qwelyt/scorne/hardware/IDC_2x5p.stl

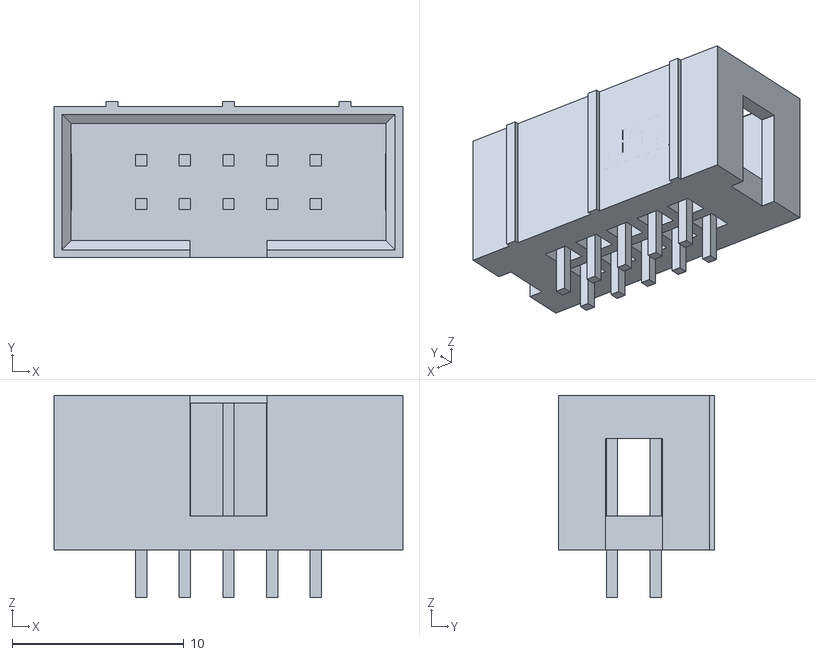
[picture p16: CAD file, 2021-04-13]
hardware/IDC_2x5p.stl
20.3 x 9.10 x 11.8
