qwelyt/scorne/hardware/scorne.stl

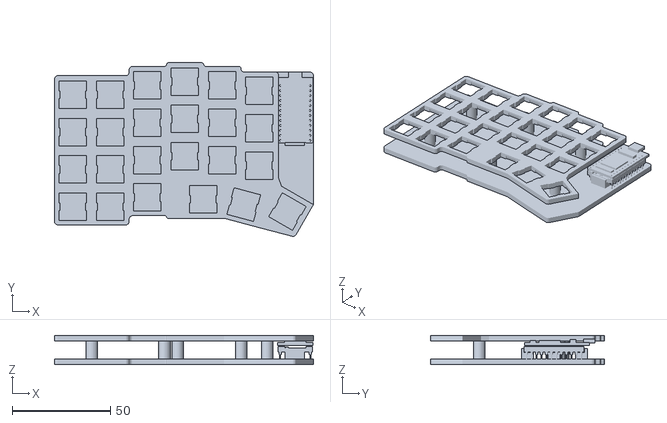
[picture p17: CAD file, 2021-03-25]
hardware/scorne.stl
132.1 x 88.6 x 15.0
