qwelyt/scorne/hardware/proMicro.stl

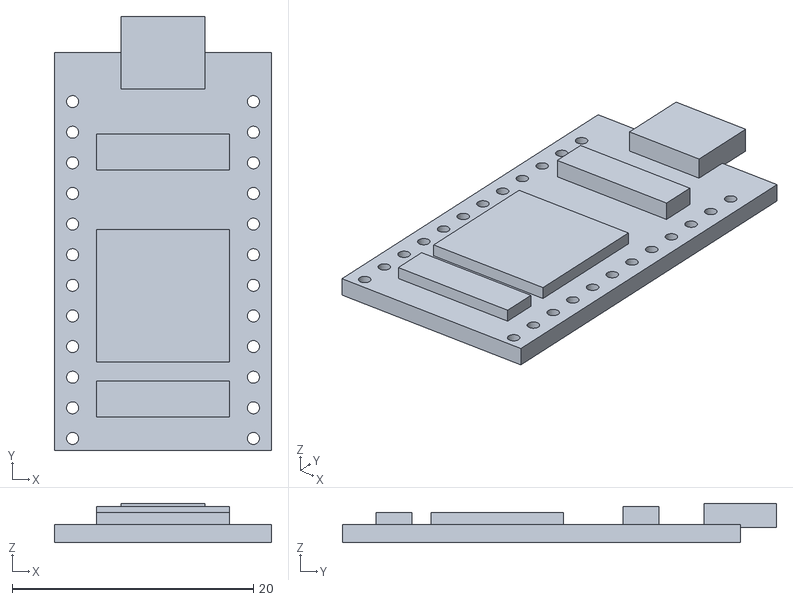
[picture p18: CAD file, 2021-03-25]
hardware/proMicro.stl
18.0 x 36.0 x 3.25
