qwelyt/scorne/hardware/socket.stl

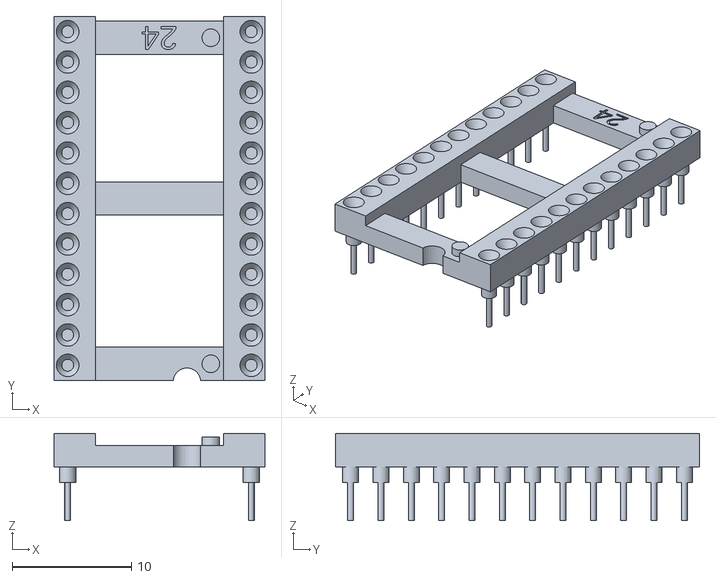
[picture p19: CAD file, 2021-03-25]
hardware/socket.stl
17.7 x 30.5 x 7.29
