qwelyt/scorne/hardware/pinHeader.stl

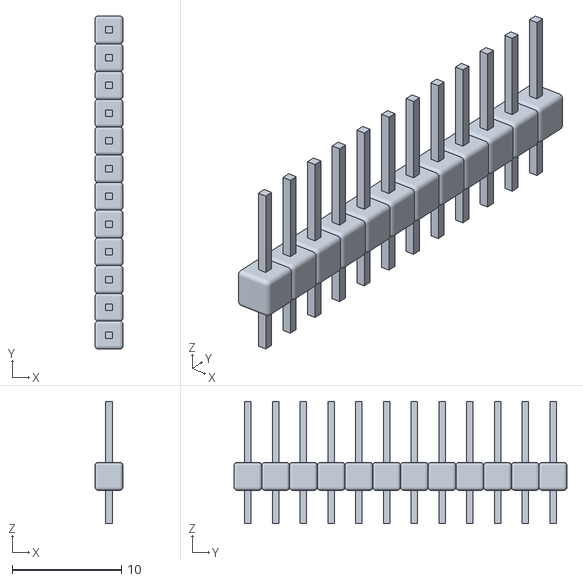
[picture p20: CAD file, 2021-03-25]
hardware/pinHeader.stl
2.56 x 30.5 x 11.2
