qwelyt/scorne/firmware/scorne/Keyboard.cpp

#include <Arduino.h>
#include <HID.h>
#include "Keyboard.h"

const byte REPORT_ID = 0x02;

void send6KRO(byte, byte[]);

static const byte hidReportDescriptor[] PROGMEM = {

  //  Keyboard
  0x05, 0x01,                    // USAGE_PAGE (Generic Desktop)
  0x09, 0x06,                    // USAGE (Keyboard)
  0xa1, 0x01,                    // COLLECTION (Application)
  0x85, REPORT_ID,               //   REPORT_ID (2)
  0x05, 0x07,                    //   USAGE_PAGE (Keyboard)

  0x19, 0xe0,                    //   USAGE_MINIMUM (Keyboard LeftControl)
  0x29, 0xe7,                    //   USAGE_MAXIMUM (Keyboard RightGUI)
  0x15, 0x00,                    //   LOGICAL_MINIMUM (0)
  0x25, 0x01,                    //   LOGICAL_MAXIMUM (1)
  0x75, 0x01,                    //   REPORT_SIZE (1)

  0x95, 0x08,                      //   REPORT_COUNT (8)
  0x81, 0x02,                    //   INPUT (Data,Var,Abs)
  0x95, 0x01,                    //   REPORT_COUNT (1)
  0x75, 0x08,                    //   REPORT_SIZE (8)
  0x81, 0x03,                    //   INPUT (Cnst,Var,Abs)

  0x95, 0x06,                      //   REPORT_COUNT (6)
  0x75, 0x08,                    //   REPORT_SIZE (8)
  0x15, 0x00,                    //   LOGICAL_MINIMUM (0)
  0x25, 0x65,                    //   LOGICAL_MAXIMUM (101)
  0x05, 0x07,                    //   USAGE_PAGE (Keyboard)

  0x19, 0x00,                      //   USAGE_MINIMUM (Reserved (no event indicated))
  0x29, 0x65,                    //   USAGE_MAXIMUM (Keyboard Application)
  0x81, 0x00,                    //   INPUT (Data,Ary,Abs)
  0xc0,                          // END_COLLECTION

};

typedef struct {
  byte modifiers;
  byte reserved;
  byte keys[6];
} KeyReport;


void initKeyboard() {
  HIDSubDescriptor node(hidReportDescriptor, sizeof(hidReportDescriptor));
  HID().AppendDescriptor(&node);
}

void sendKeyBuffer(byte meta, byte keys[], byte keyLimit) {
  if(keyLimit == 6) {
    send6KRO(meta, keys);
  } else {
    // No idea. But should probably figure out how to do a NKRO.
  }
}

void send6KRO(byte meta, byte keys[]){
  KeyReport report;

  report.modifiers = meta;

  for (byte b = 0; b < 6; ++b) {
    report.keys[b] = keys[b];
  }
  HID().SendReport(REPORT_ID, &report, sizeof(report));
}
